whowechina/bishi_pico/Reference/Bishi-Bashi-for-Sale-in-Singapore.jpg

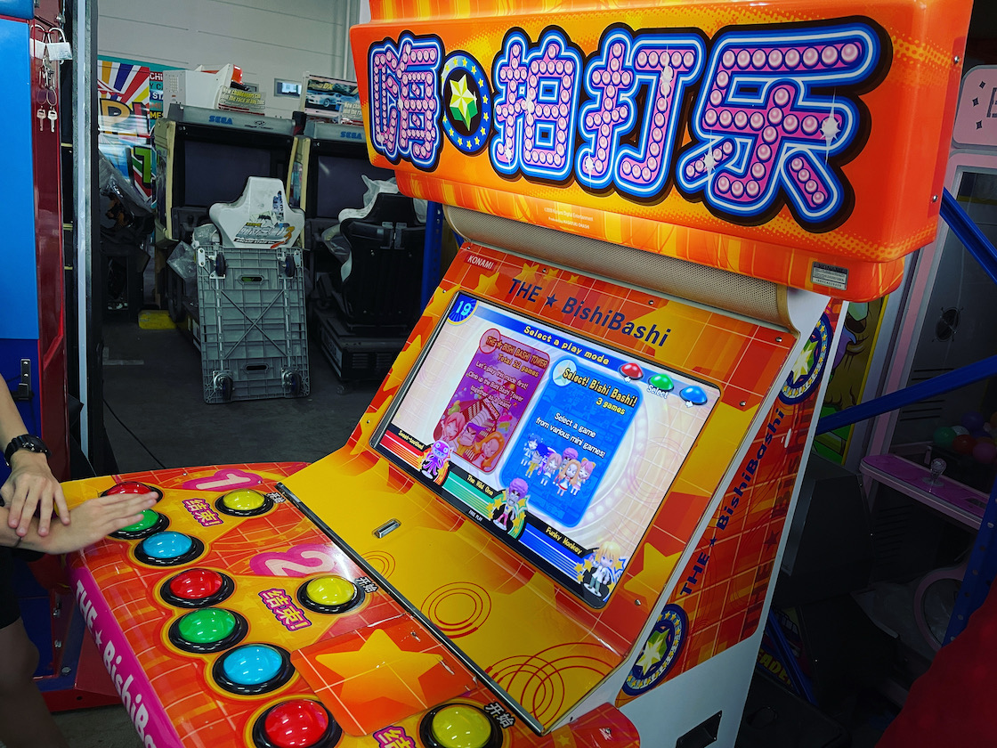
Reference/Bishi-Bashi-for-Sale-in-Singapore.jpg
