whowechina/bishi_pico/Reference/bishi-bashi-is-such-a-fun-machine-for-party-games-v0-jovngem12dkb1.webp

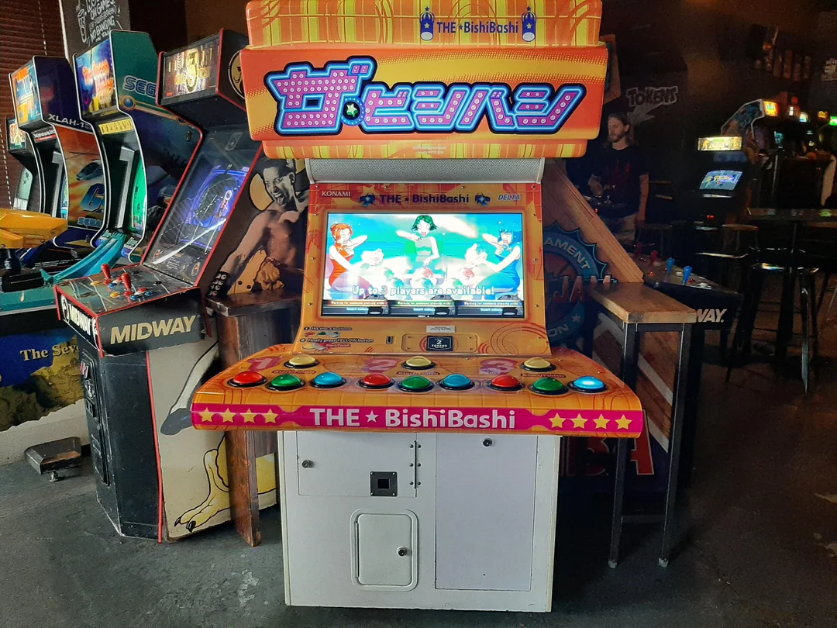
Reference/bishi-bashi-is-such-a-fun-machine-for-party-games-v0-jovngem12dkb1.webp
