whowechina/bishi_pico/Reference/Bishi_Bashi_Channel.webp

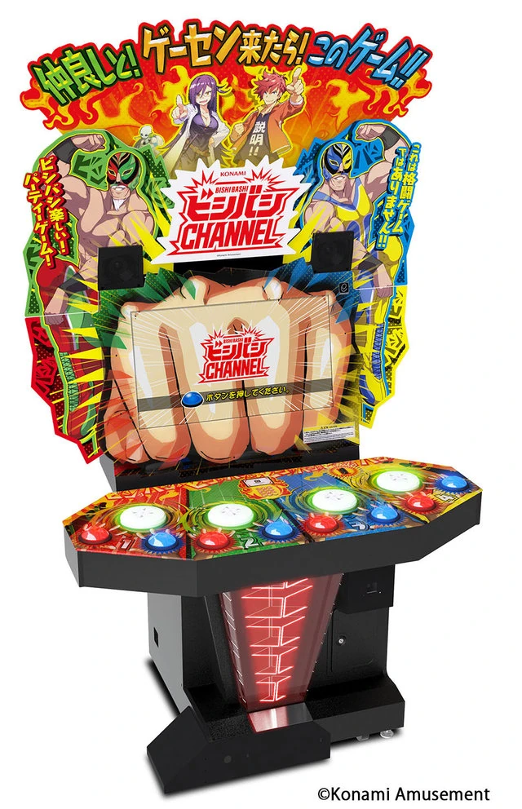
Reference/Bishi_Bashi_Channel.webp
