whowechina/bishi_pico/PCB/3dmodels/User Library-PTS645SL95SMTR92-LFS.STEP

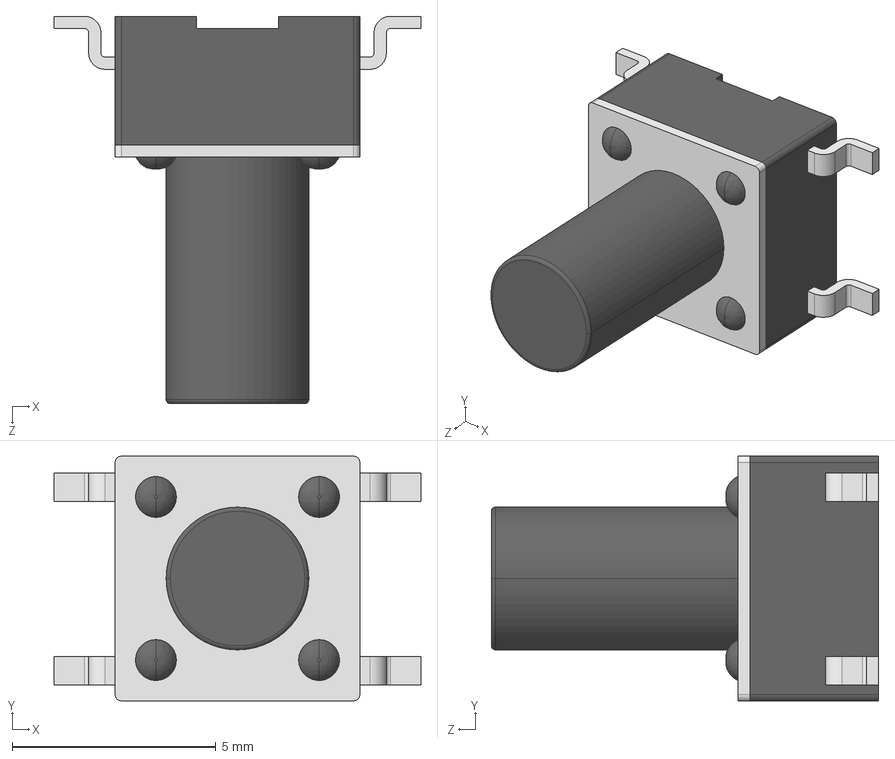
[picture p32: CAD file, 2024-11-27]
PCB/3dmodels/User Library-PTS645SL95SMTR92-LFS.STEP
9.00 x 6.00 x 9.50 mm
