whowechina/bishi_pico/Production/3DPrint/bishi_mag_seat.stl

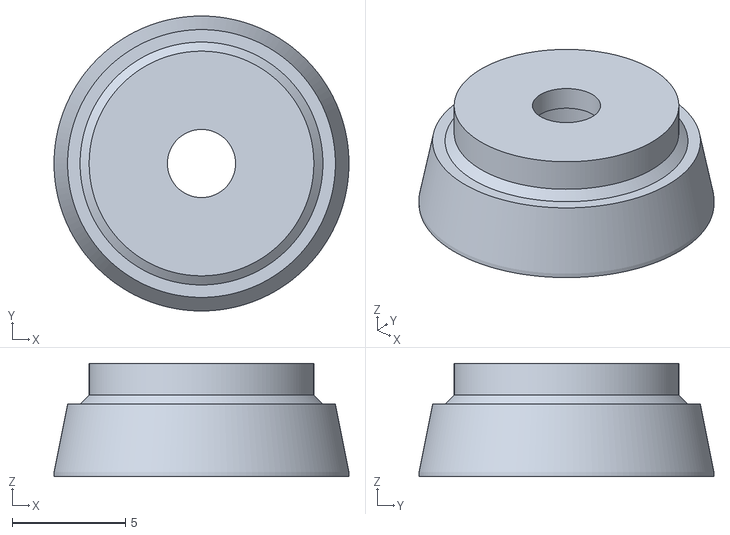
[picture p33: CAD file, 2024-12-17]
Production/3DPrint/bishi_mag_seat.stl
13.0 x 13.0 x 5.00
