whowechina/bishi_pico/PCB/3dmodels/Slider.step

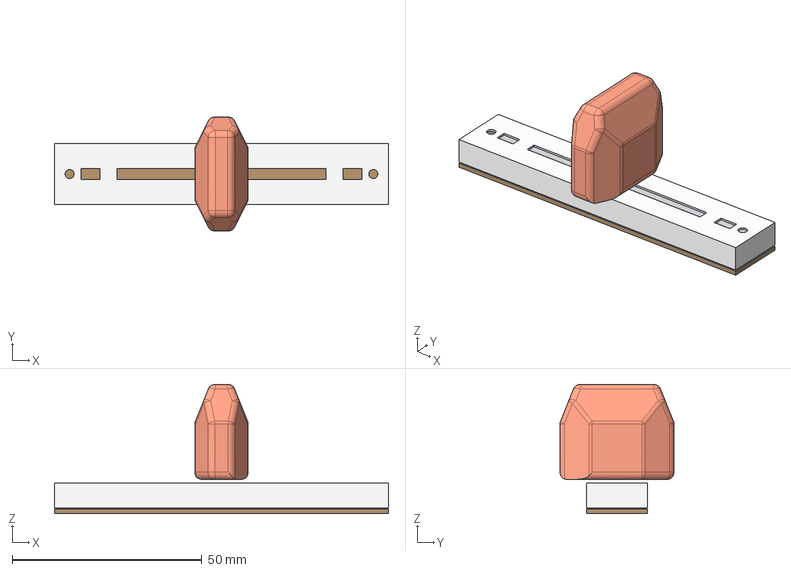
[picture p34: CAD file, 2024-11-27]
PCB/3dmodels/Slider.step
88.0 x 30.0 x 34.0 mm
