whowechina/bishi_pico/Production/3DPrint/bishi_support.stl

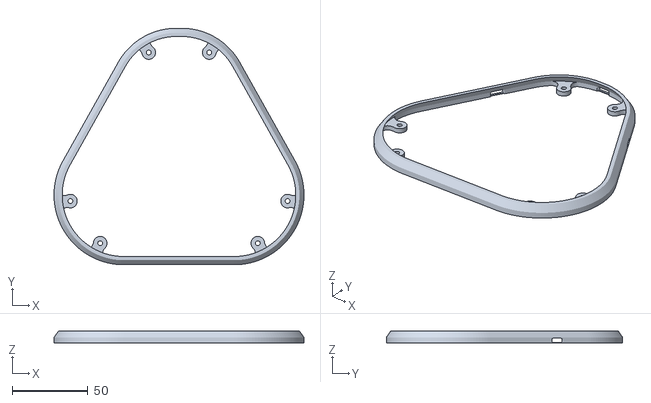
[picture p35: CAD file, 2024-12-17]
Production/3DPrint/bishi_support.stl
164.9 x 156.0 x 8.00
