whowechina/bishi_pico/PCB/3dmodels/Kailh_PG1353.STEP

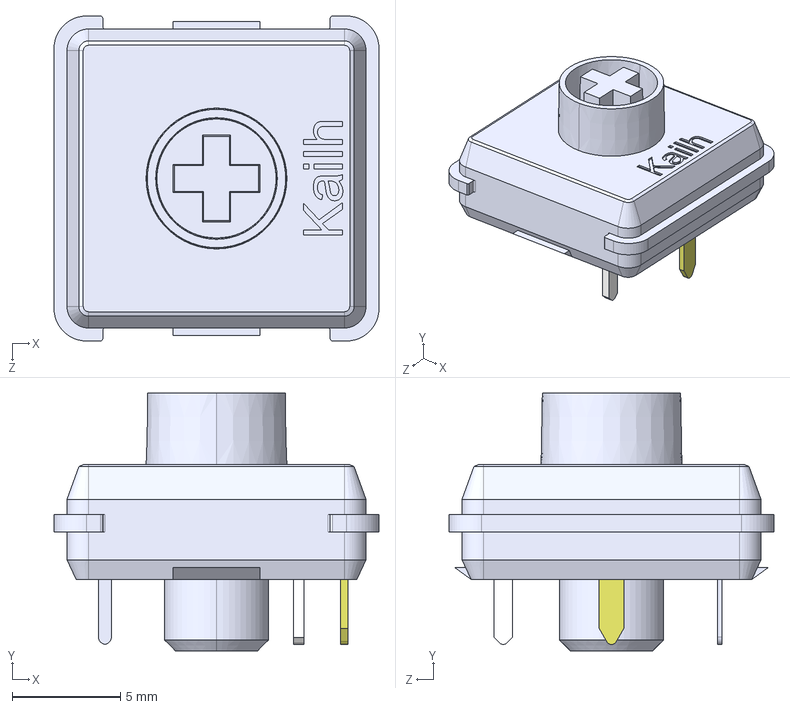
[picture p36: CAD file, 2024-11-27]
PCB/3dmodels/Kailh_PG1353.STEP
15.0 x 11.9 x 15.0 mm
