whowechina/bishi_pico/PCB/3dmodels/SMD WS2812B-3535.step

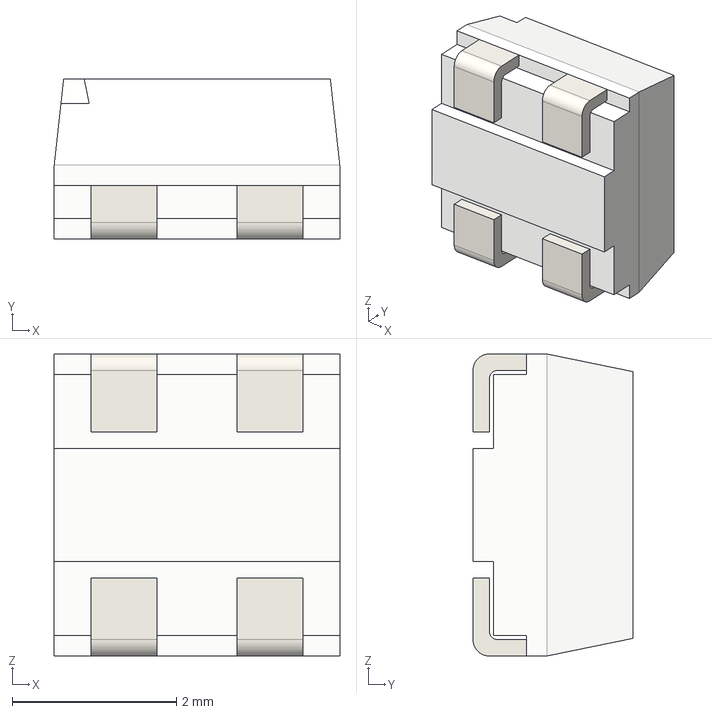
[picture p37: CAD file, 2024-11-27]
PCB/3dmodels/SMD WS2812B-3535.step
3.48 x 1.95 x 3.68 mm
