whowechina/bishi_pico/PCB/3dmodels/SS49E.step

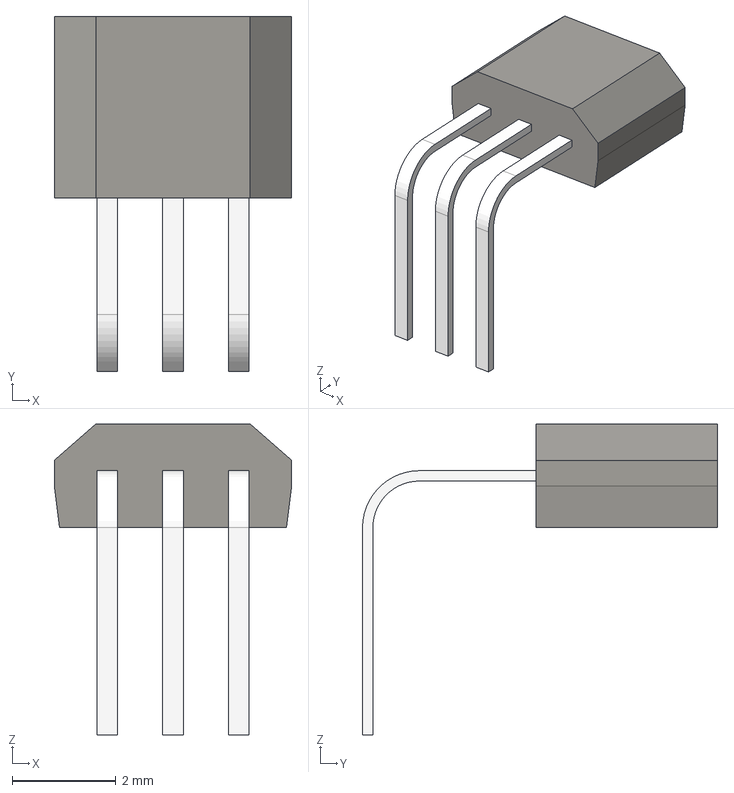
[picture p38: CAD file, 2024-11-27]
PCB/3dmodels/SS49E.step
4.58 x 6.85 x 6.00 mm
