whowechina/bishi_pico/PCB/3dmodels/mpr121_breakout_v13.stl

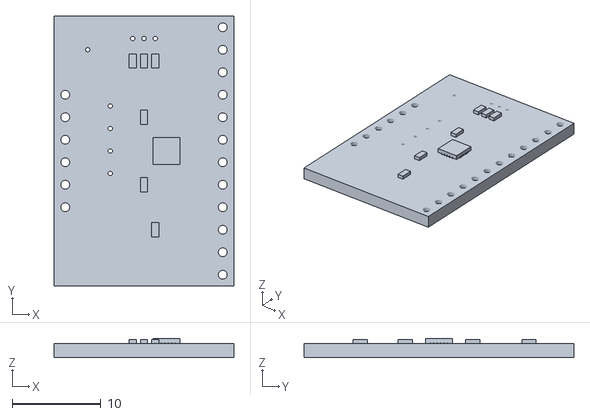
[picture p39: CAD file, 2024-11-27]
PCB/3dmodels/mpr121_breakout_v13.stl
20.3 x 30.5 x 2.20
