whowechina/bishi_pico/PCB/3dmodels/FPC0.5MM1.0H18P.step

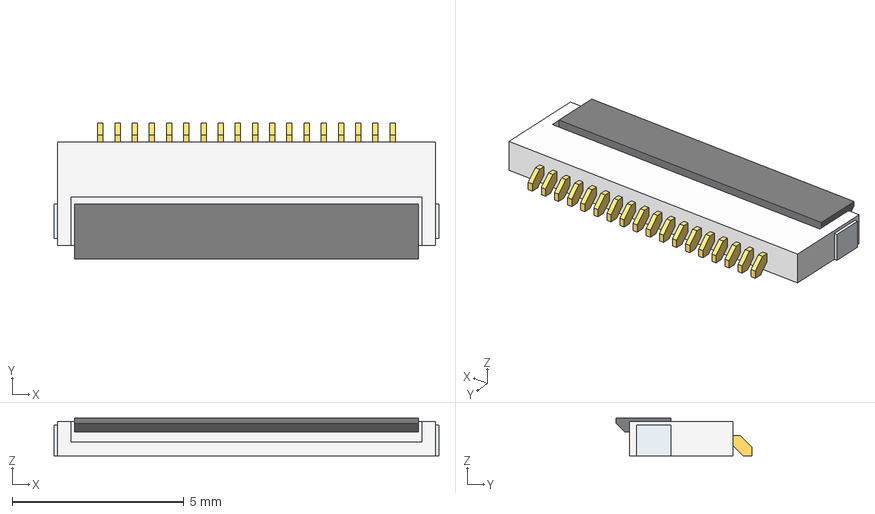
[picture p40: CAD file, 2024-11-27]
PCB/3dmodels/FPC0.5MM1.0H18P.step
11.2 x 3.96 x 1.10 mm
