whowechina/bishi_pico/PCB/3dmodels/User Library-WS2812-4020.step

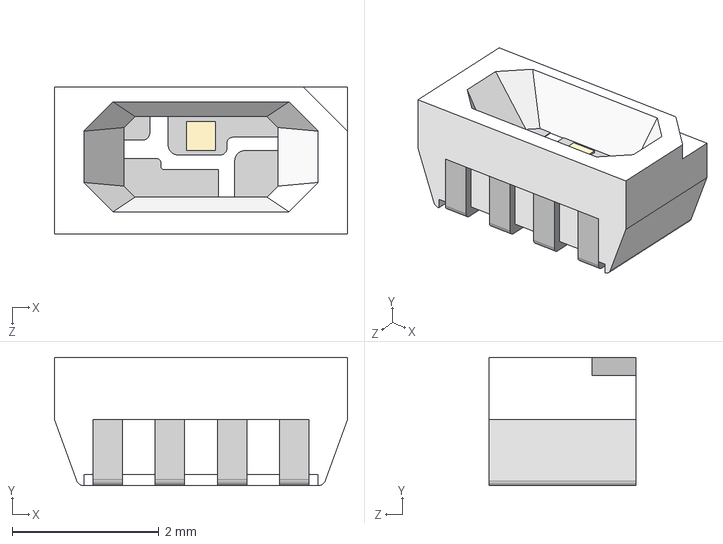
[picture p41: CAD file, 2024-11-27]
PCB/3dmodels/User Library-WS2812-4020.step
4.00 x 1.75 x 2.00 mm
