whowechina/bishi_pico/PCB/3dmodels/pn5180.step

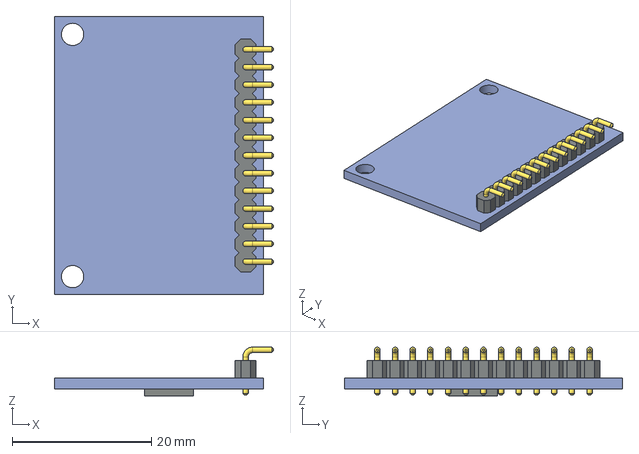
[picture p42: CAD file, 2024-11-27]
PCB/3dmodels/pn5180.step
31.5 x 40.0 x 7.00 mm
