whowechina/bishi_pico/PCB/3dmodels/WS2812-2020.STEP

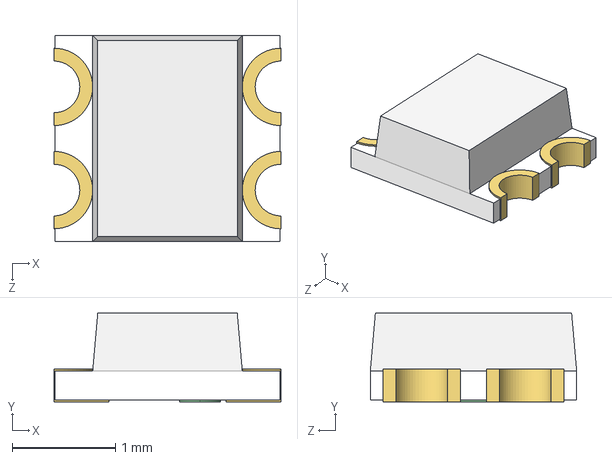
[picture p43: CAD file, 2024-11-27]
PCB/3dmodels/WS2812-2020.STEP
2.20 x 0.86 x 2.00 mm
