whowechina/bishi_pico/PCB/3dmodels/SKRRABE010.stp

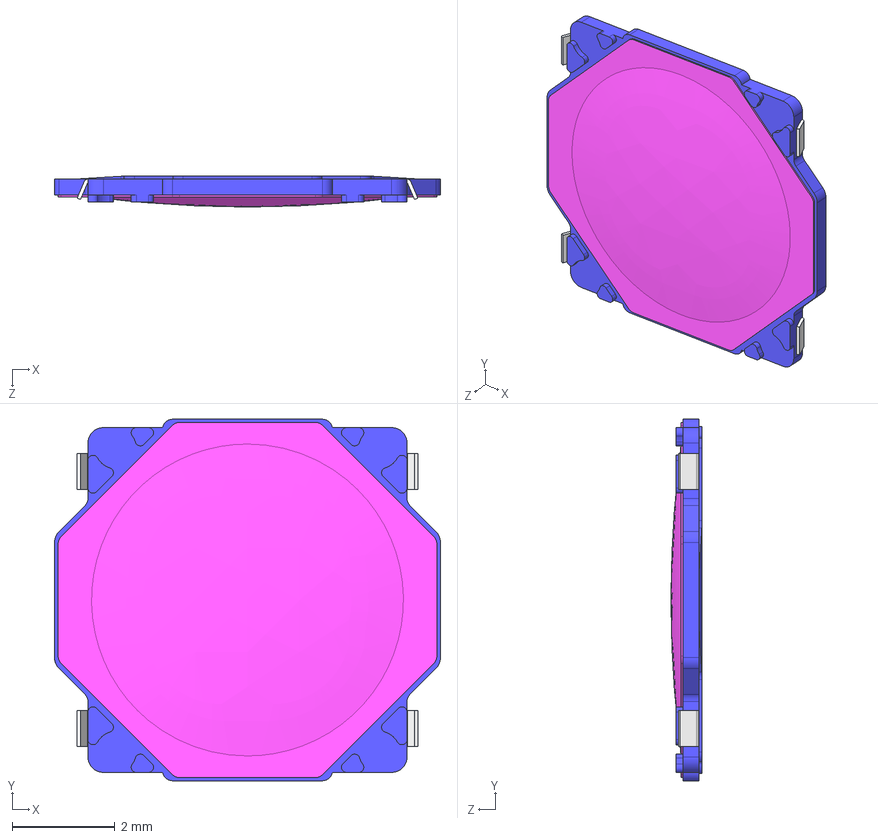
[picture p44: CAD file, 2024-11-27]
PCB/3dmodels/SKRRABE010.stp
7.50 x 7.03 x 0.6 mm
