whowechina/bishi_pico/PCB/3dmodels/SPEAKER_SMD_1340.STEP

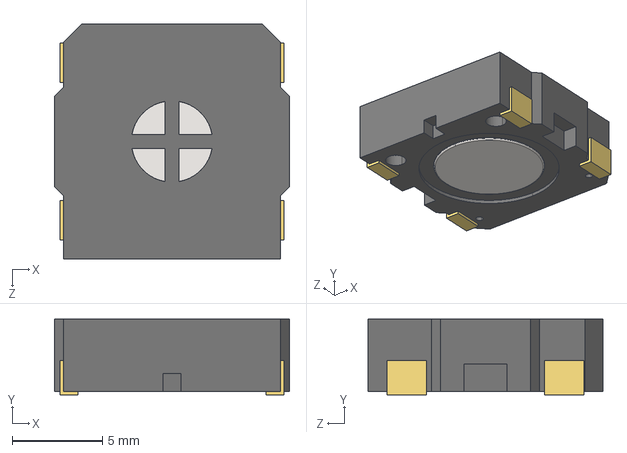
[picture p45: CAD file, 2024-11-27]
PCB/3dmodels/SPEAKER_SMD_1340.STEP
13.0 x 4.20 x 13.0 mm
