whowechina/bishi_pico/PCB/3dmodels/SW_Kailh_Choc_V1.stp

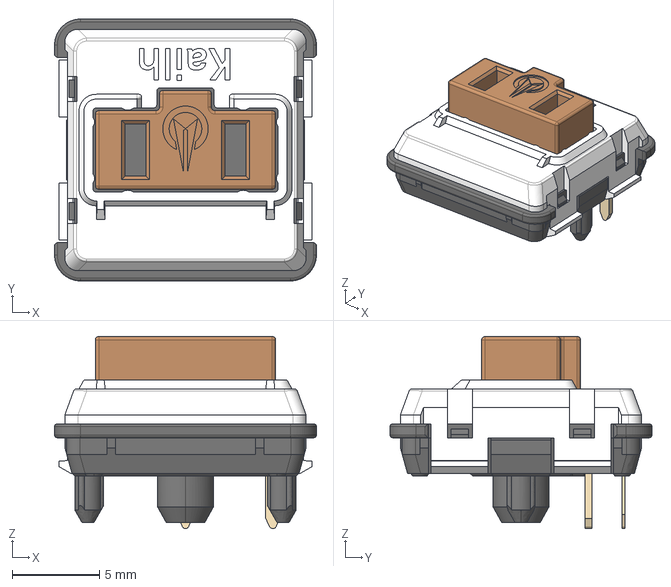
[picture p46: CAD file, 2024-11-27]
PCB/3dmodels/SW_Kailh_Choc_V1.stp
15.0 x 15.0 x 11.0 mm
