whowechina/bishi_pico/PCB/3dmodels/WS2812-0807.STEP

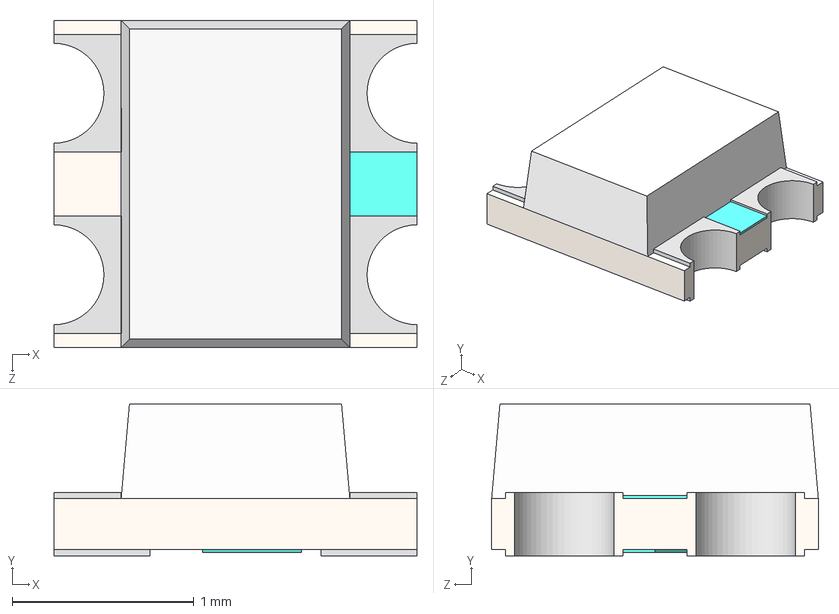
[picture p47: CAD file, 2024-11-27]
PCB/3dmodels/WS2812-0807.STEP
2.00 x 0.835 x 1.80 mm
