whowechina/bishi_pico/PCB/3dmodels/Magnetic Pogo Connector 5 Pin (Type 2).STEP

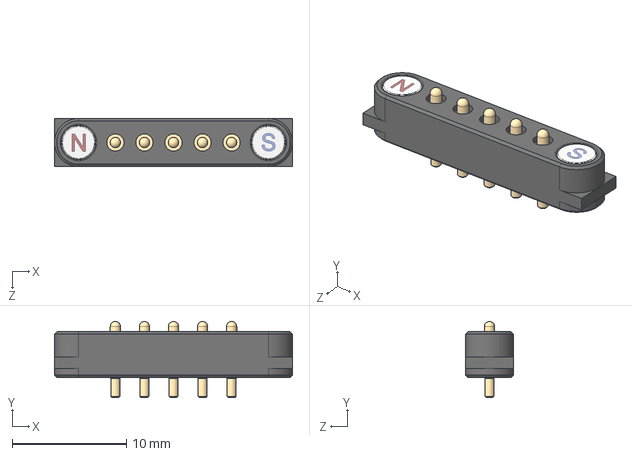
[picture p48: CAD file, 2024-11-27]
PCB/3dmodels/Magnetic Pogo Connector 5 Pin (Type 2).STEP
20.8 x 6.65 x 4.20 mm
