whowechina/bishi_pico/PCB/3dmodels/SKSTAAE010.stp

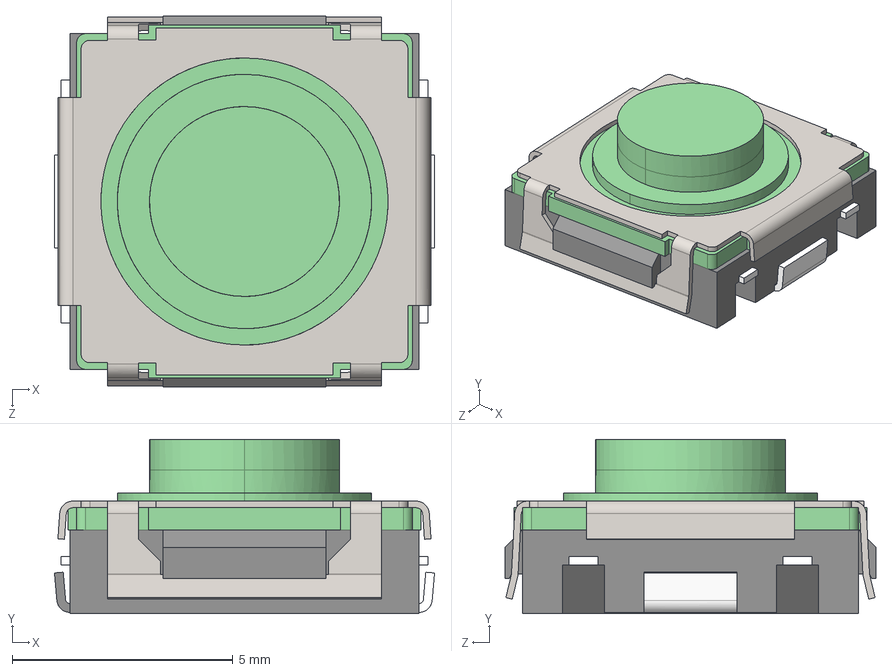
[picture p49: CAD file, 2024-11-27]
PCB/3dmodels/SKSTAAE010.stp
8.61 x 3.95 x 8.40 mm
