whowechina/bishi_pico/PCB/3dmodels/Button Cap.step

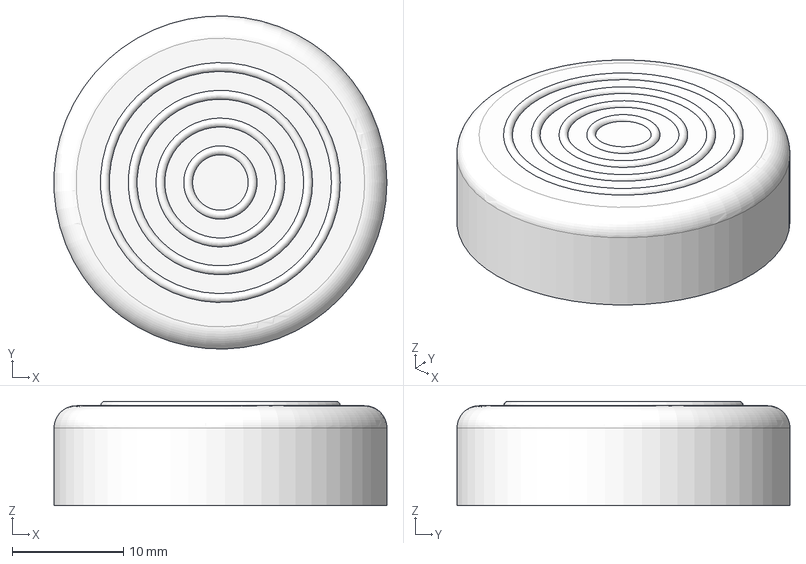
[picture p50: CAD file, 2024-11-27]
PCB/3dmodels/Button Cap.step
30.0 x 30.0 x 9.40 mm
