whowechina/bishi_pico/PCB/3dmodels/WS2812B.step

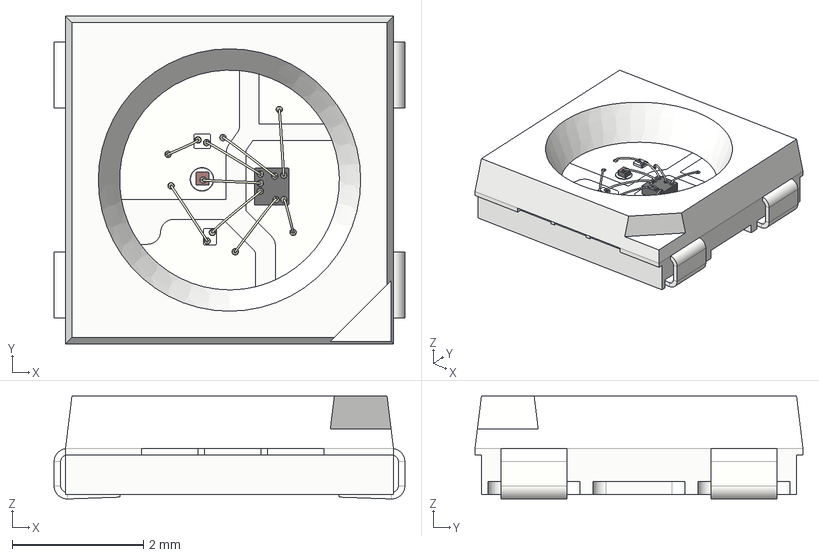
[picture p51: CAD file, 2024-11-27]
PCB/3dmodels/WS2812B.step
5.35 x 5.00 x 1.57 mm
