whowechina/bishi_pico/PCB/3dmodels/Tact Switch 4.5mm SMT.step

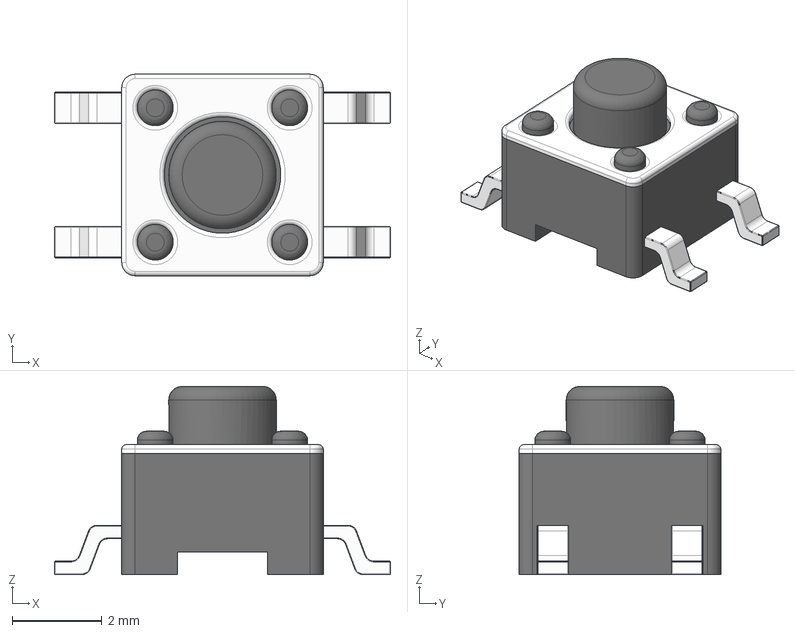
[picture p52: CAD file, 2024-11-27]
PCB/3dmodels/Tact Switch 4.5mm SMT.step
7.50 x 4.50 x 4.20 mm
