whowechina/bishi_pico/PCB/3dmodels/Magnetic Pogo Connector 5 Pin (Type 4).STEP

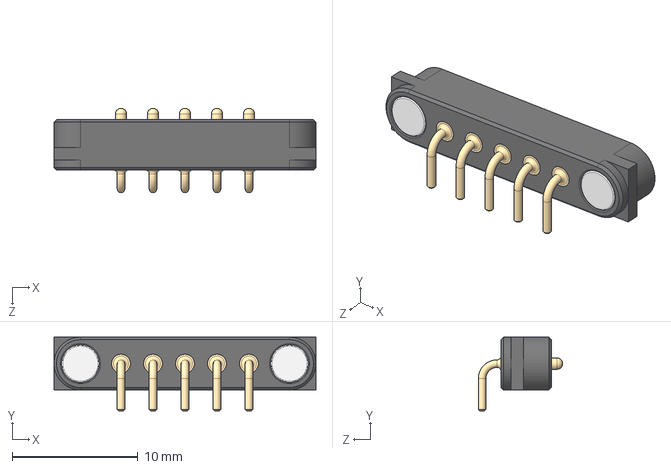
[picture p53: CAD file, 2024-11-27]
PCB/3dmodels/Magnetic Pogo Connector 5 Pin (Type 4).STEP
20.8 x 5.85 x 6.70 mm
