whowechina/bishi_pico/PCB/3dmodels/chu_keypad_lgp.step

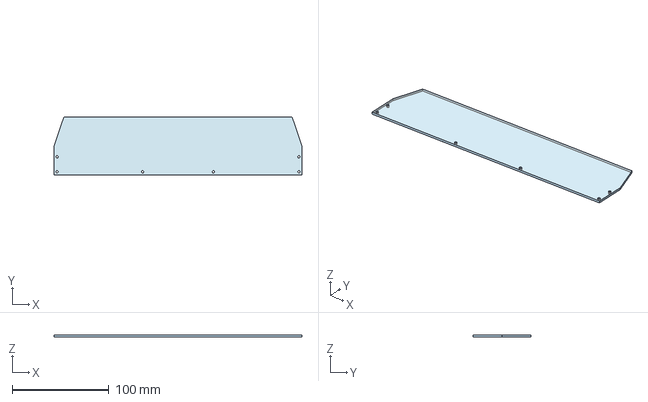
[picture p54: CAD file, 2024-11-27]
PCB/3dmodels/chu_keypad_lgp.step
256.0 x 60.0 x 2.00 mm
