whowechina/bishi_pico/PCB/3dmodels/Magnetic Pogo Connector 5 Pin (Type 3).STEP

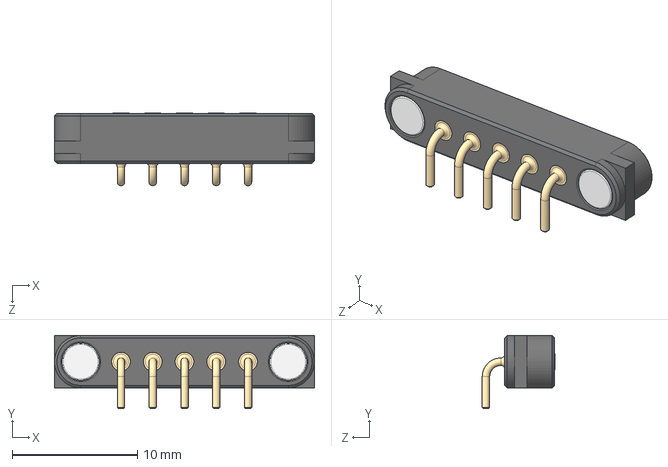
[picture p55: CAD file, 2024-11-27]
PCB/3dmodels/Magnetic Pogo Connector 5 Pin (Type 3).STEP
20.8 x 5.85 x 5.80 mm
