whowechina/bishi_pico/PCB/3dmodels/User Library-RGB1204.STEP

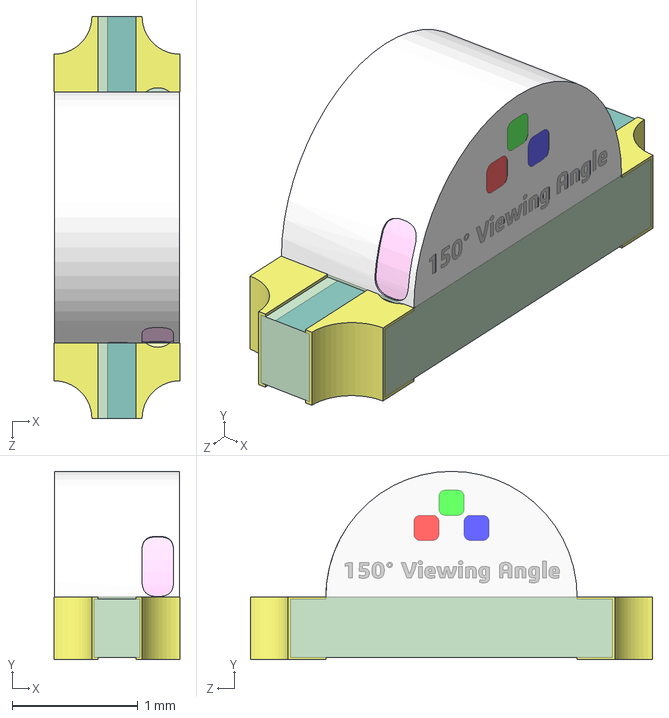
[picture p56: CAD file, 2024-11-27]
PCB/3dmodels/User Library-RGB1204.STEP
1.00 x 1.50 x 3.20 mm
