whowechina/bishi_pico/PCB/3dmodels/SM04B-SRSS-TB.STEP

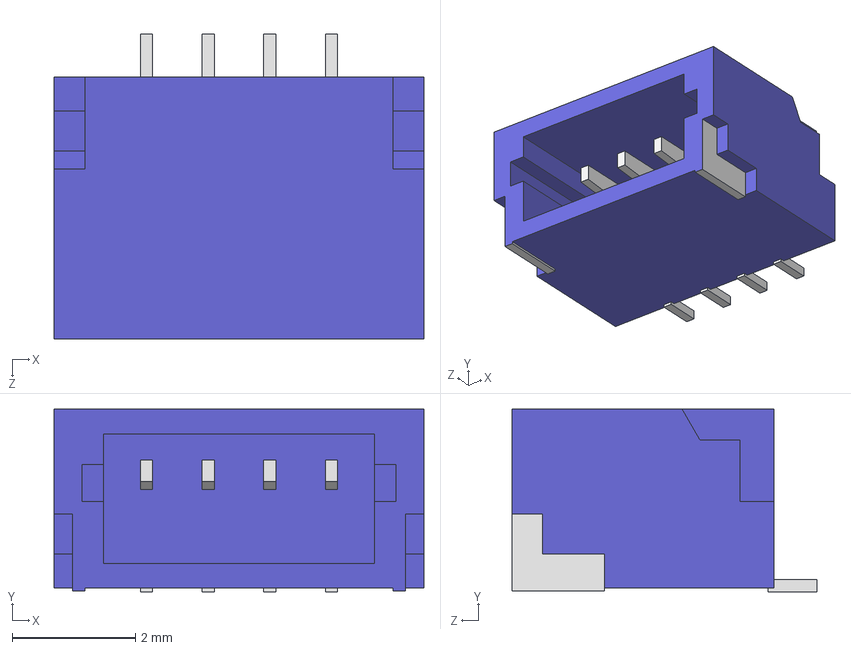
[picture p57: CAD file, 2024-11-27]
PCB/3dmodels/SM04B-SRSS-TB.STEP
6.00 x 2.96 x 4.95 mm
