whowechina/bishi_pico/PCB/3dmodels/Kailh Polia.step

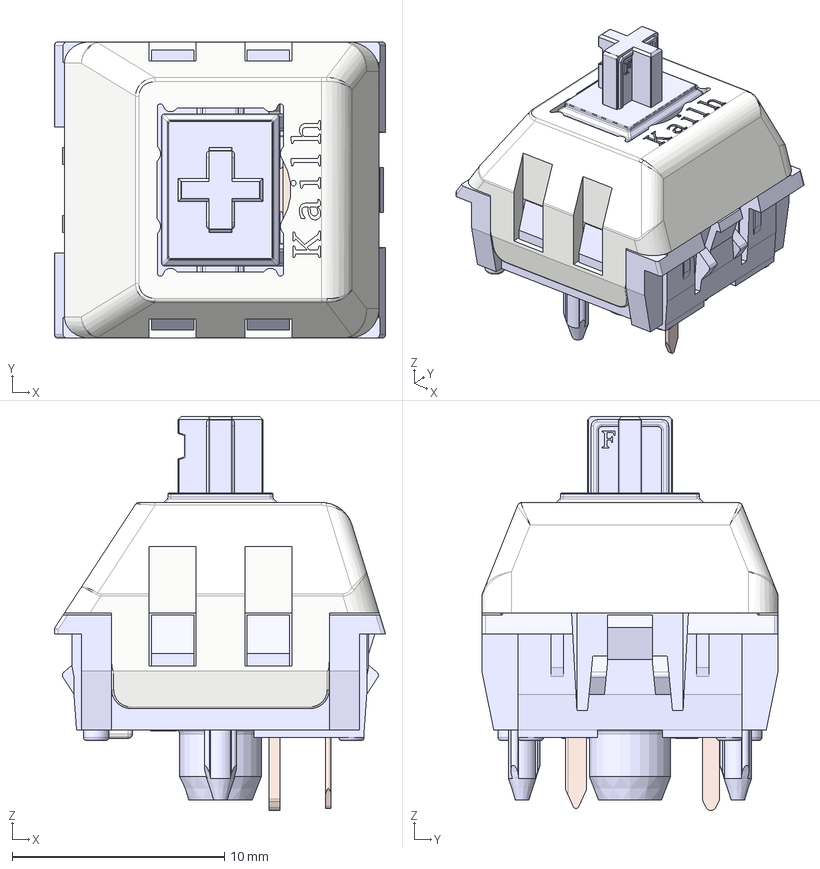
[picture p58: CAD file, 2024-11-27]
PCB/3dmodels/Kailh Polia.step
15.6 x 14.0 x 18.5 mm
Housing
ThickContact
SpringContact
Stem
Lid
