whowechina/bishi_pico/PCB/3dmodels/SW_Hotswap_Kailh_MX.stp

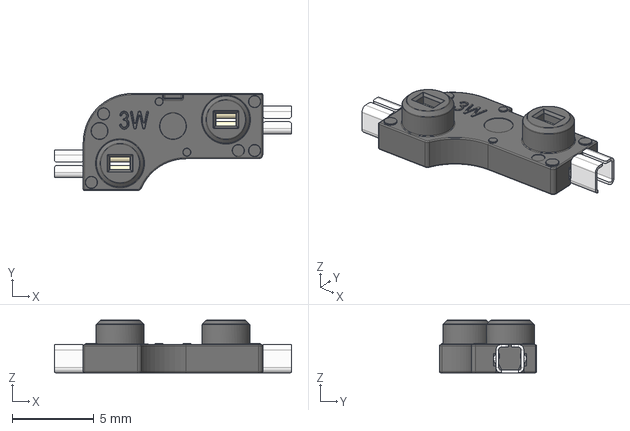
[picture p59: CAD file, 2024-11-27]
PCB/3dmodels/SW_Hotswap_Kailh_MX.stp
14.5 x 5.95 x 3.22 mm
