whowechina/bishi_pico/PCB/3dmodels/geki_button.step

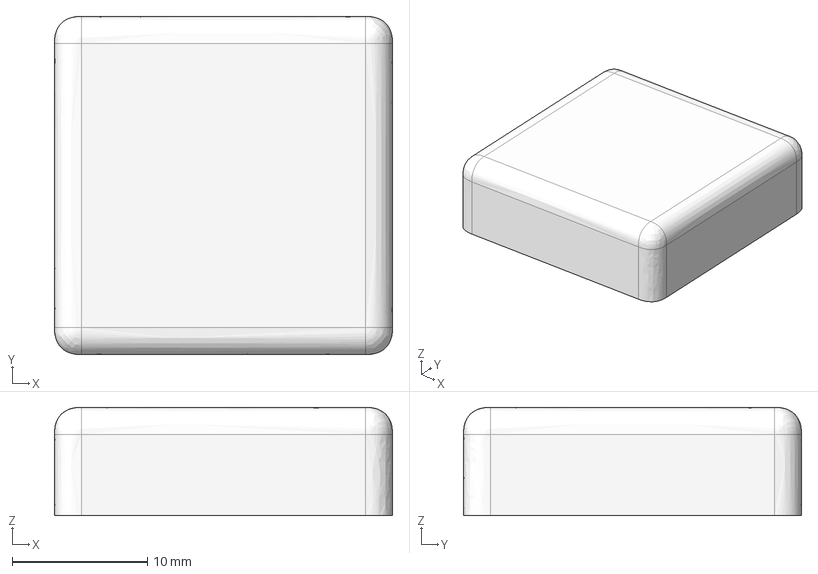
[picture p60: CAD file, 2024-11-27]
PCB/3dmodels/geki_button.step
25.0 x 25.0 x 8.00 mm
