whowechina/bishi_pico/PCB/3dmodels/gp2y0e03.3mf

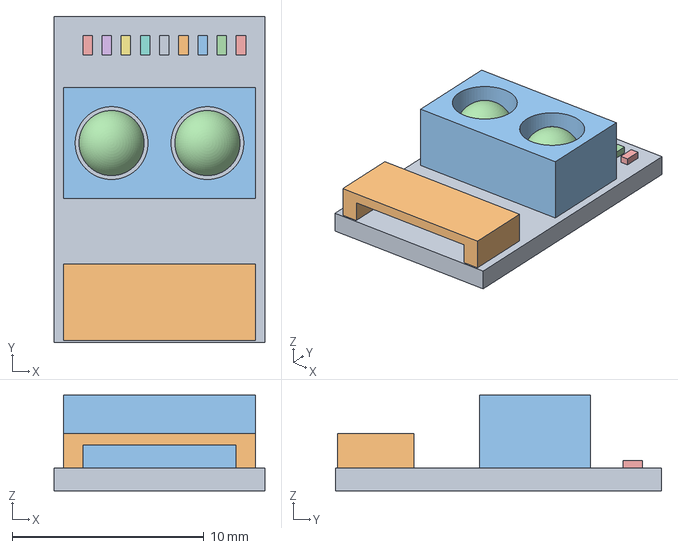
[picture p61: CAD file, 2024-11-27]
PCB/3dmodels/gp2y0e03.3mf
11.0 x 17.0 x 5.00 mm
