whowechina/bishi_pico/PCB/3dmodels/J 2835.step

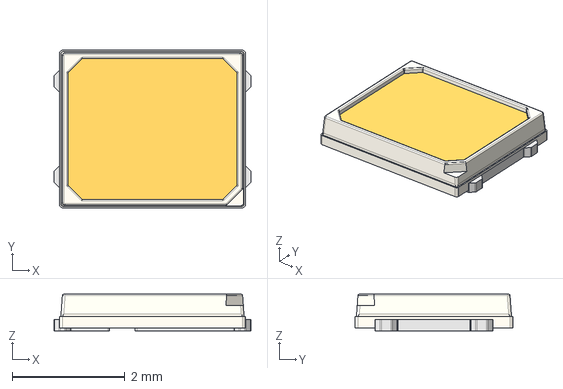
[picture p62: CAD file, 2024-11-27]
PCB/3dmodels/J 2835.step
3.50 x 2.80 x 0.65 mm
