whowechina/bishi_pico/PCB/3dmodels/dcdc_3to5.step

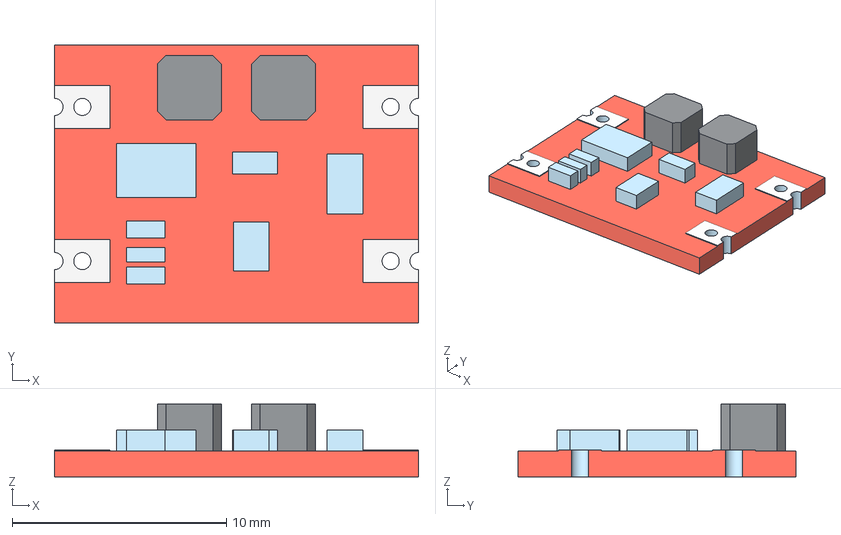
[picture p63: CAD file, 2024-11-27]
PCB/3dmodels/dcdc_3to5.step
17.0 x 13.0 x 3.40 mm
