whowechina/bishi_pico/PCB/3dmodels/Kailh LP Choc PC Keycap.step

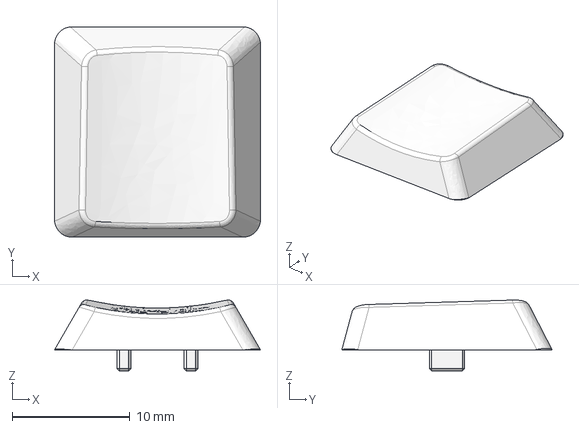
[picture p64: CAD file, 2024-11-27]
PCB/3dmodels/Kailh LP Choc PC Keycap.step
17.5 x 17.9 x 6.03 mm
