whowechina/bishi_pico/PCB/3dmodels/Geki_Slider.step

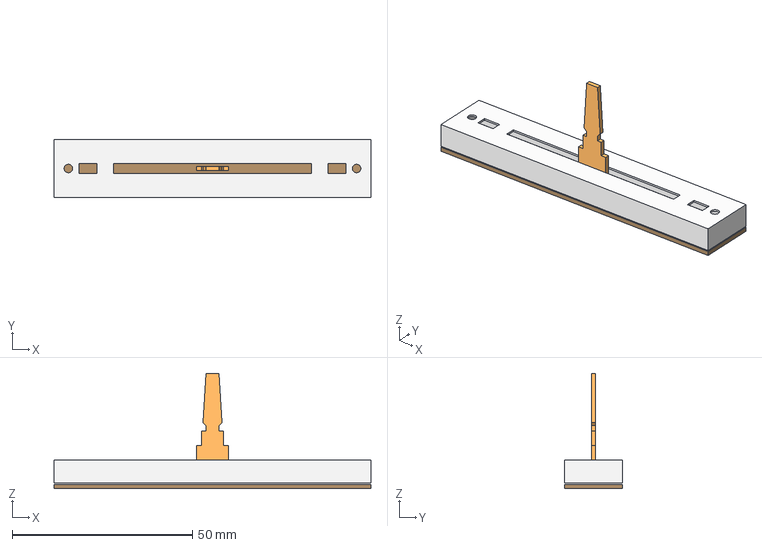
[picture p65: CAD file, 2024-11-27]
PCB/3dmodels/Geki_Slider.step
88.0 x 16.0 x 32.0 mm
