whowechina/bishi_pico/PCB/3dmodels/TRS Jack PJ-313.stp

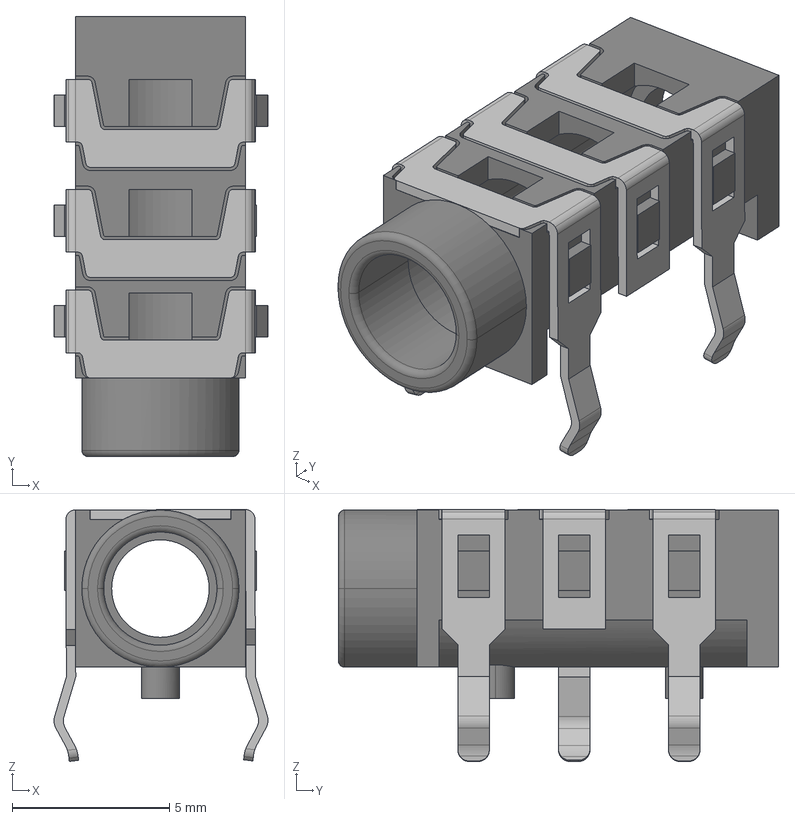
[picture p66: CAD file, 2024-11-27]
PCB/3dmodels/TRS Jack PJ-313.stp
6.81 x 14.0 x 8.02 mm
