whowechina/bishi_pico/PCB/3dmodels/8002A.step

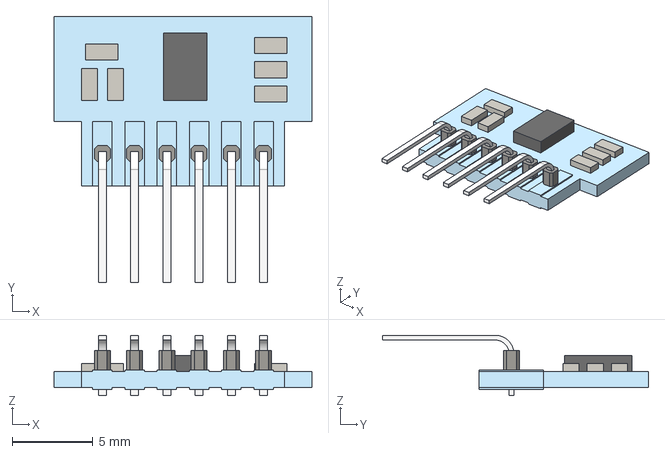
[picture p67: CAD file, 2024-11-27]
PCB/3dmodels/8002A.step
16.0 x 16.5 x 3.75 mm
