whowechina/bishi_pico/PCB/3dmodels/User Library-WS2812-2020.step

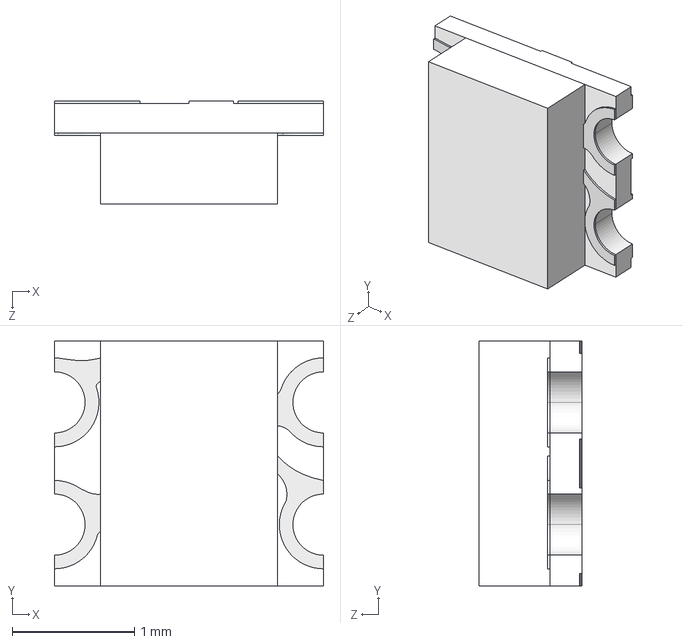
[picture p68: CAD file, 2024-11-27]
PCB/3dmodels/User Library-WS2812-2020.step
2.20 x 2.00 x 0.84 mm
