whowechina/bishi_pico/PCB/3dmodels/User Library-pj-393-8.STEP

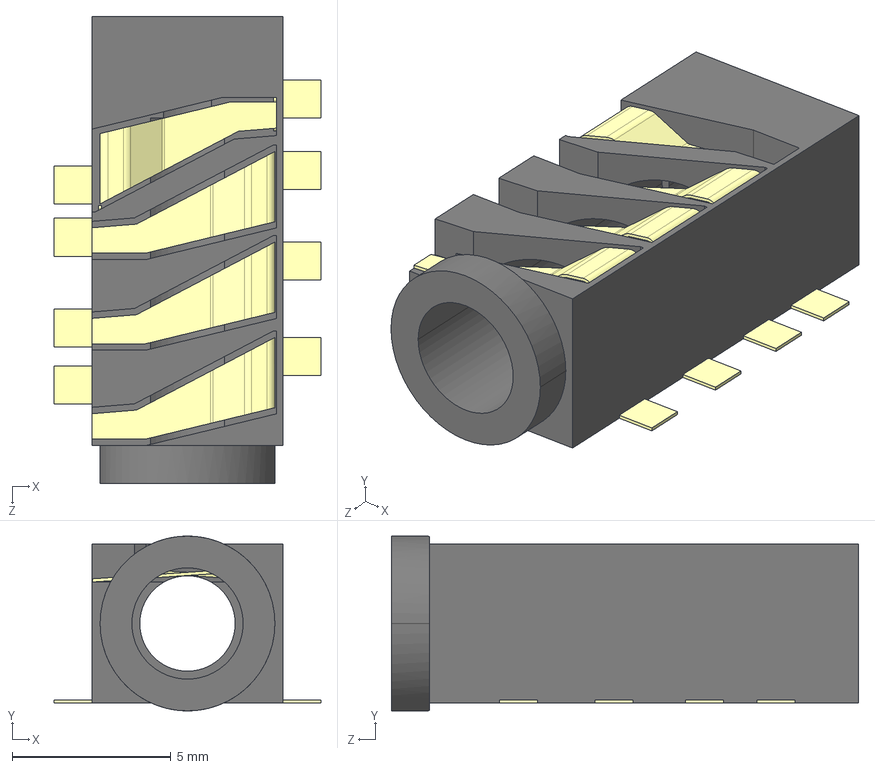
[picture p69: CAD file, 2024-11-27]
PCB/3dmodels/User Library-pj-393-8.STEP
8.40 x 5.50 x 14.7 mm
PJ-393-8_1
PJ-393-8_2 x 4
PJ-393-8_3
PJ-393-8_4 x 3
