whowechina/bishi_pico/PCB/3dmodels/SKPMAM.STEP

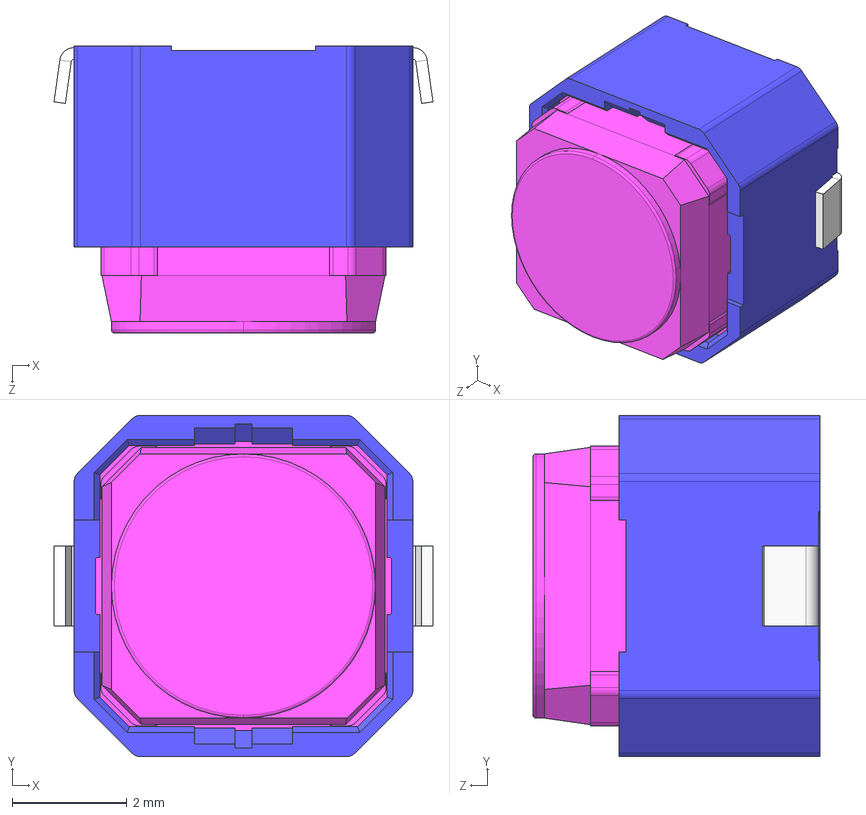
[picture p70: CAD file, 2024-11-27]
PCB/3dmodels/SKPMAM.STEP
6.60 x 5.94 x 5.00 mm
